FrankBoesing/FlexiBoard/extras/ESP8266/esp-12_ce.jpg

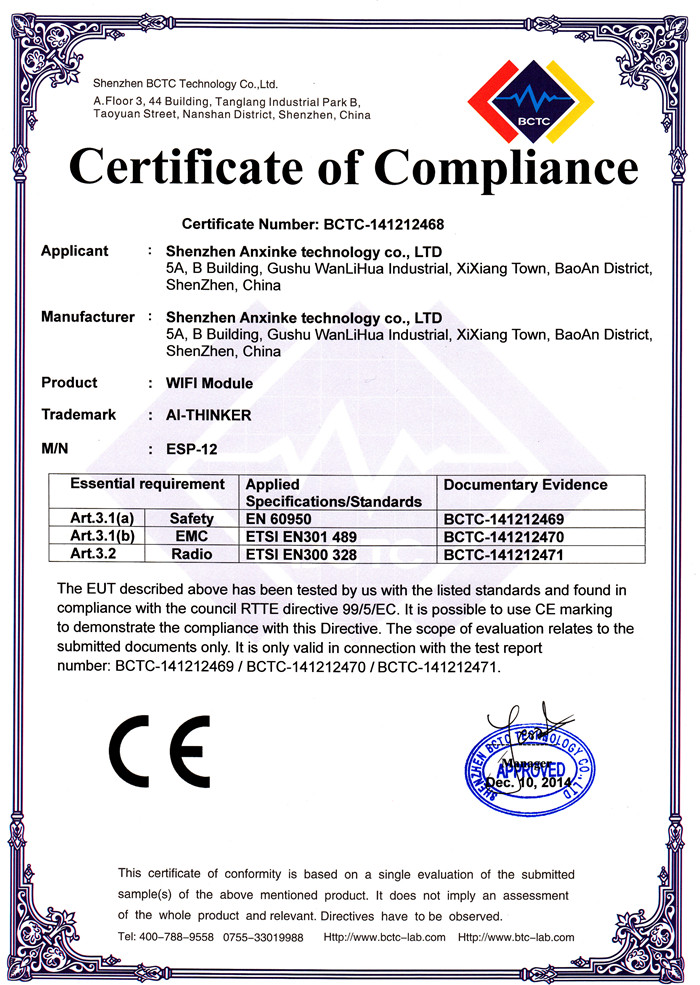
extras/ESP8266/esp-12_ce.jpg
