FrankBoesing/FlexiBoard/extras/ESP8266/esp-12_fcc1.jpg

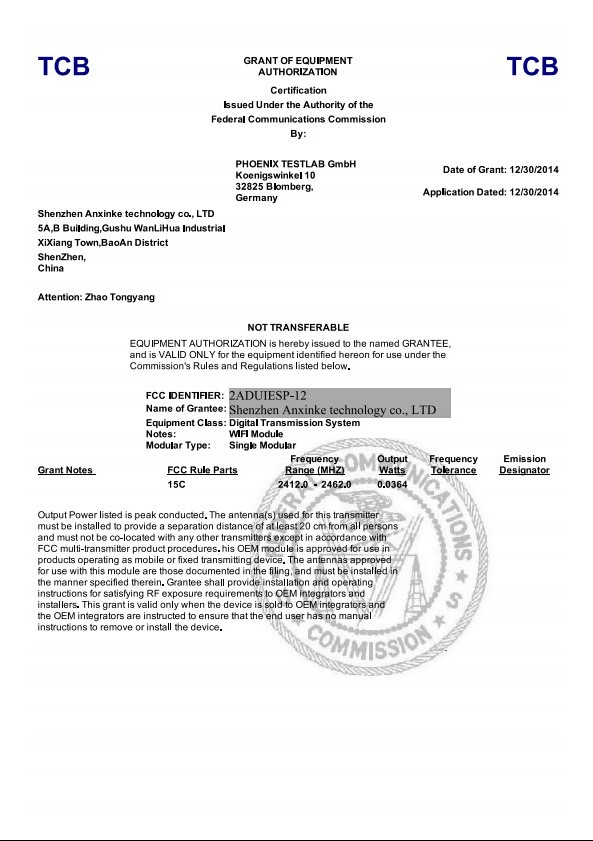
extras/ESP8266/esp-12_fcc1.jpg
