FrankBoesing/FlexiBoard/extras/ESP8266/esp-12_fcc2.jpg

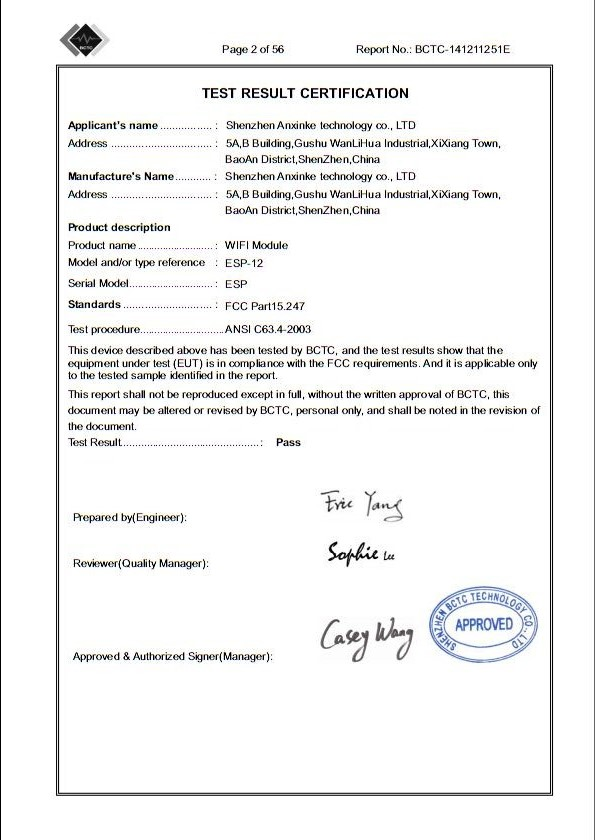
extras/ESP8266/esp-12_fcc2.jpg
