FrankBoesing/FlexiBoard/extras/ESP8266/esp-12_pindef.png

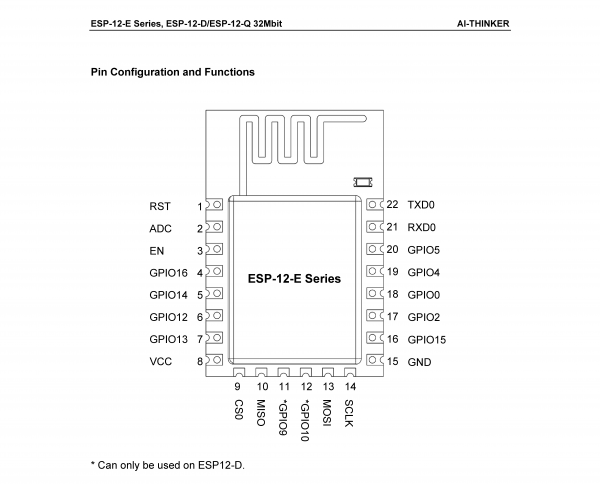
extras/ESP8266/esp-12_pindef.png
