FrankBoesing/FlexiBoard/extras/RTL8710/FWIFS25IRLQHUGK.MEDIUM.jpg

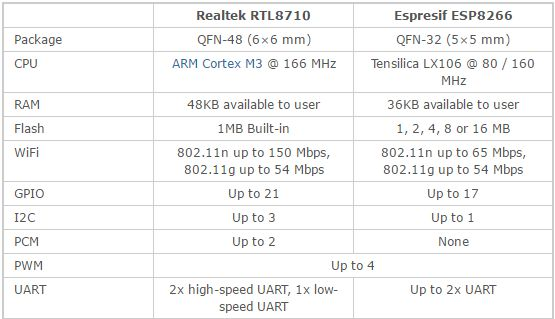
extras/RTL8710/FWIFS25IRLQHUGK.MEDIUM.jpg
