FrankBoesing/FlexiBoard/src/examples/FlexiBoard_T3tris/font_BlackOpsOne-Regular.h

#ifndef font_BlackOpsOne 
#define font_BlackOpsOne 
 
#include "ILI9341_t3.h"

#ifdef __cplusplus 
extern "C" {
#endif

extern const ILI9341_t3_font_t BlackOpsOne_8;
extern const ILI9341_t3_font_t BlackOpsOne_9;
extern const ILI9341_t3_font_t BlackOpsOne_10;
extern const ILI9341_t3_font_t BlackOpsOne_11;
extern const ILI9341_t3_font_t BlackOpsOne_12;
extern const ILI9341_t3_font_t BlackOpsOne_13;
extern const ILI9341_t3_font_t BlackOpsOne_14;
extern const ILI9341_t3_font_t BlackOpsOne_16;
extern const ILI9341_t3_font_t BlackOpsOne_18;
extern const ILI9341_t3_font_t BlackOpsOne_20;
extern const ILI9341_t3_font_t BlackOpsOne_24;
extern const ILI9341_t3_font_t BlackOpsOne_28;
extern const ILI9341_t3_font_t BlackOpsOne_32;
extern const ILI9341_t3_font_t BlackOpsOne_40;
extern const ILI9341_t3_font_t BlackOpsOne_48;
extern const ILI9341_t3_font_t BlackOpsOne_60;
extern const ILI9341_t3_font_t BlackOpsOne_72;
extern const ILI9341_t3_font_t BlackOpsOne_96;

#ifdef __cplusplus
} // extern "C"
#endif

#endif
